anshuliyer/EuclidCam/firmware/python/IO/io_top.py

import sys
import select

class BatteryManagement:
    """
    Manages battery-related state and hardware interfaces.
    """
    def __init__(self):
        self.battery_level = True  # Default to True as requested

class GPIOTop:
    """
    Manages top-level GPIO hardware settings (e.g. Flash).
    """
    def __init__(self):
        self.flash_setting = True  # Default to True as requested

class KeyboardInterface:
    """
    Stubs keyboard input to simulate GPIO button presses.
    """
    def get_input(self):
        """
        Returns "SPACE", "ENTER", or None.
        """
        if select.select([sys.stdin], [], [], 0)[0]:
            line = sys.stdin.readline().rstrip("\r\n")
            # If line is exactly a space, or contains 's', it's a SPACE command
            if " " in line or "s" in line.lower():
                return "SPACE"
            # Otherwise, any other input (like just hitting Enter) is ENTER
            return "ENTER"
        return None
